X-Microsystems/xmicro-bus/Images/Gen 2/Display 1.jpg

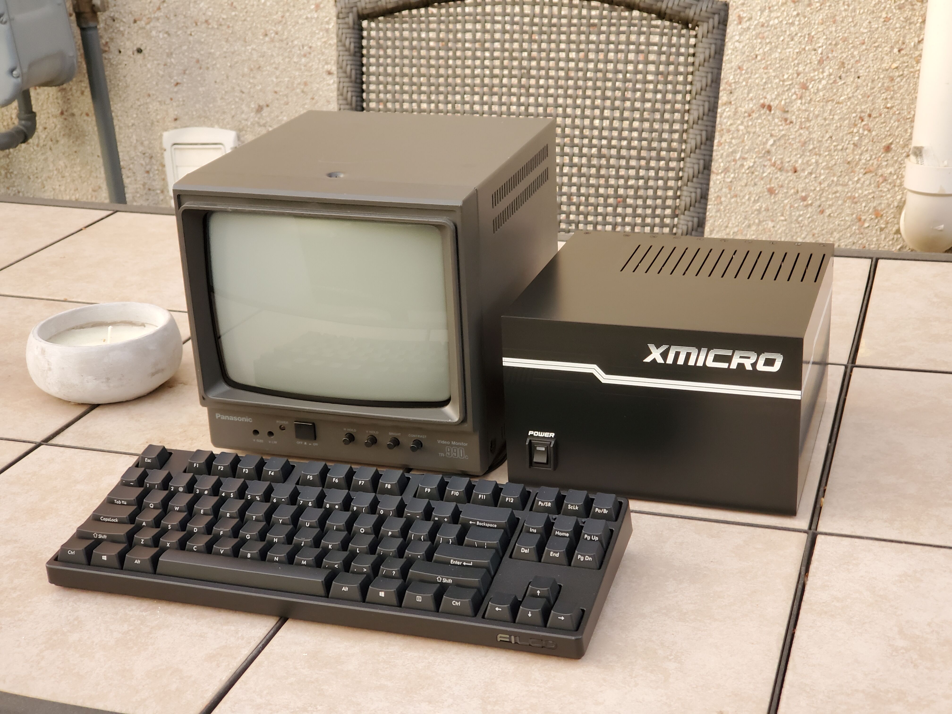
Images/Gen 2/Display 1.jpg
