X-Microsystems/xmicro-bus/Images/Gen 2/Display 2.jpg

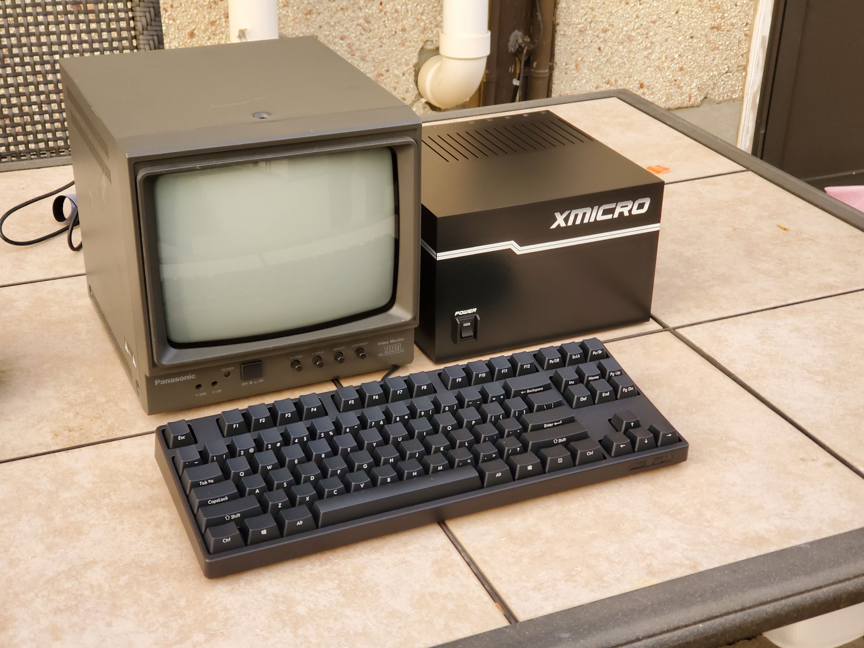
Images/Gen 2/Display 2.jpg
