X-Microsystems/xmicro-bus/Images/Gen 2/Display 3.jpg

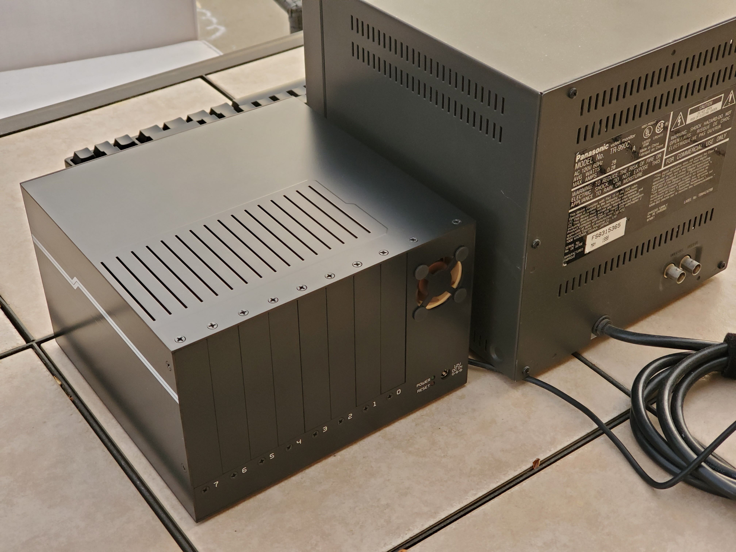
Images/Gen 2/Display 3.jpg
