X-Microsystems/xmicro-bus/Images/Gen 2/Display 5.jpg

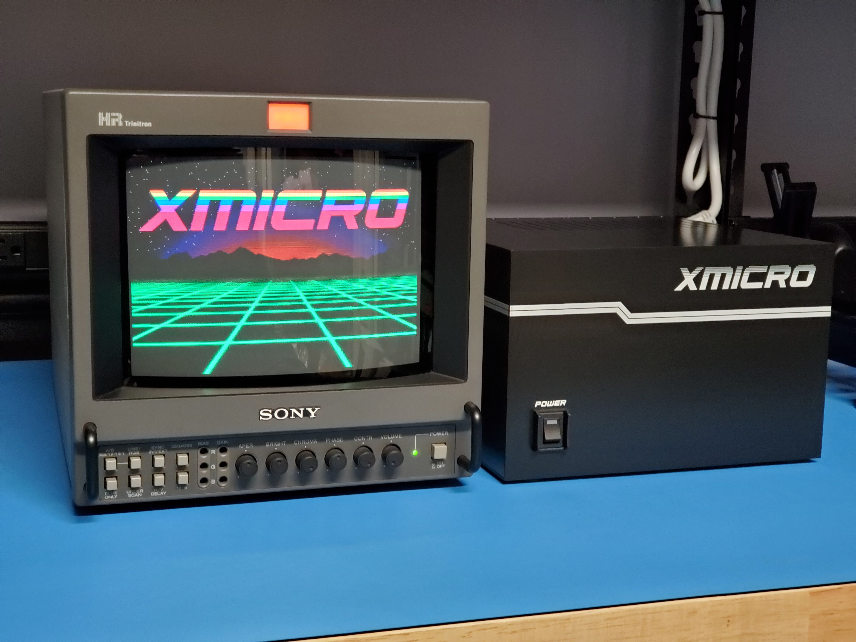
Images/Gen 2/Display 5.jpg
