X-Microsystems/xmicro-bus/Images/Gen 2/Family 2.jpg

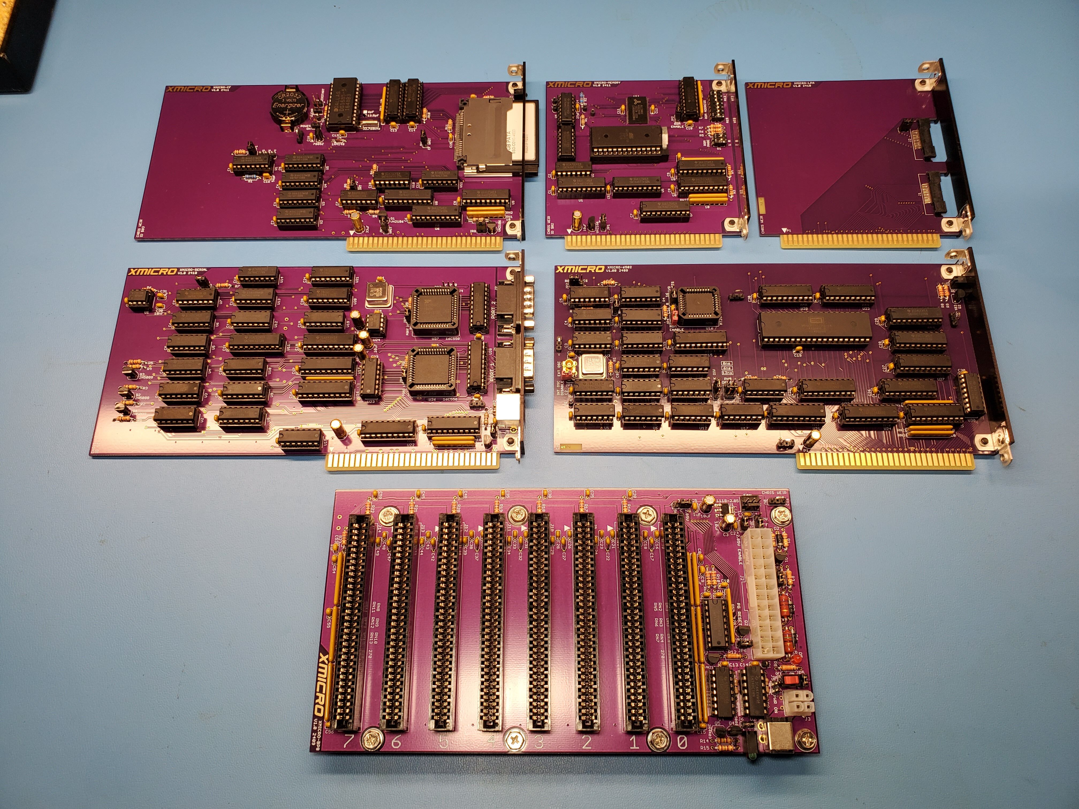
Images/Gen 2/Family 2.jpg
