X-Microsystems/xmicro-bus/Images/Gen 2/Inside 1.jpg

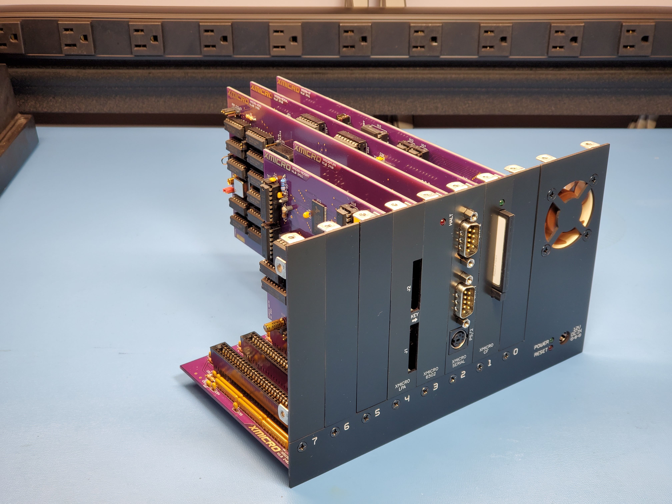
Images/Gen 2/Inside 1.jpg
