X-Microsystems/xmicro-bus/Images/Gen 2/Inside 2.jpg

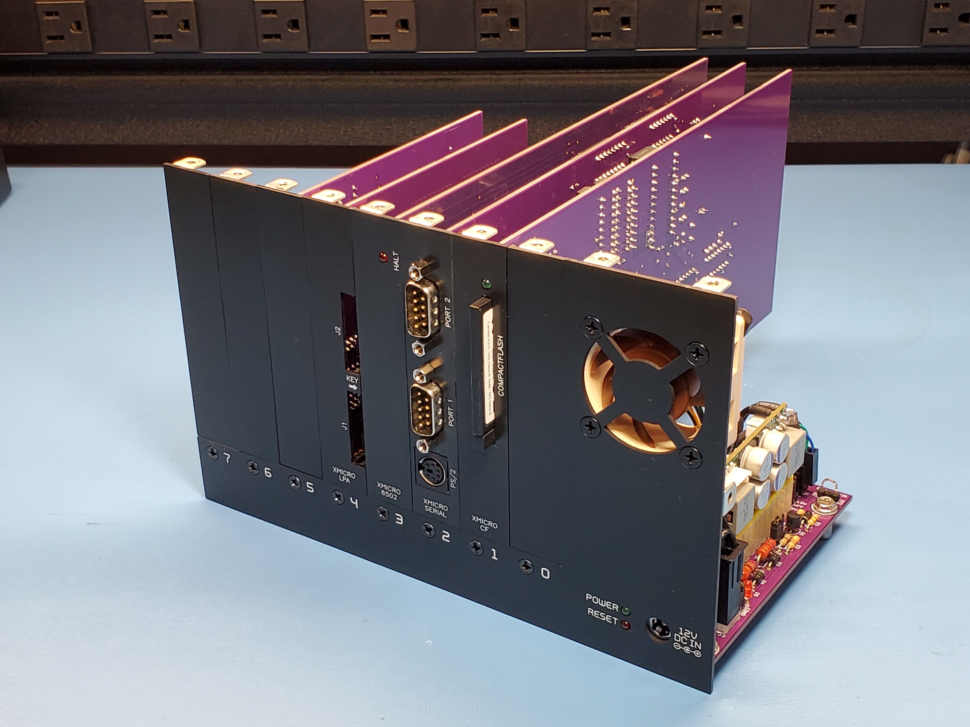
Images/Gen 2/Inside 2.jpg
