X-Microsystems/xmicro-bus/Images/Gen 2/System 1.jpg

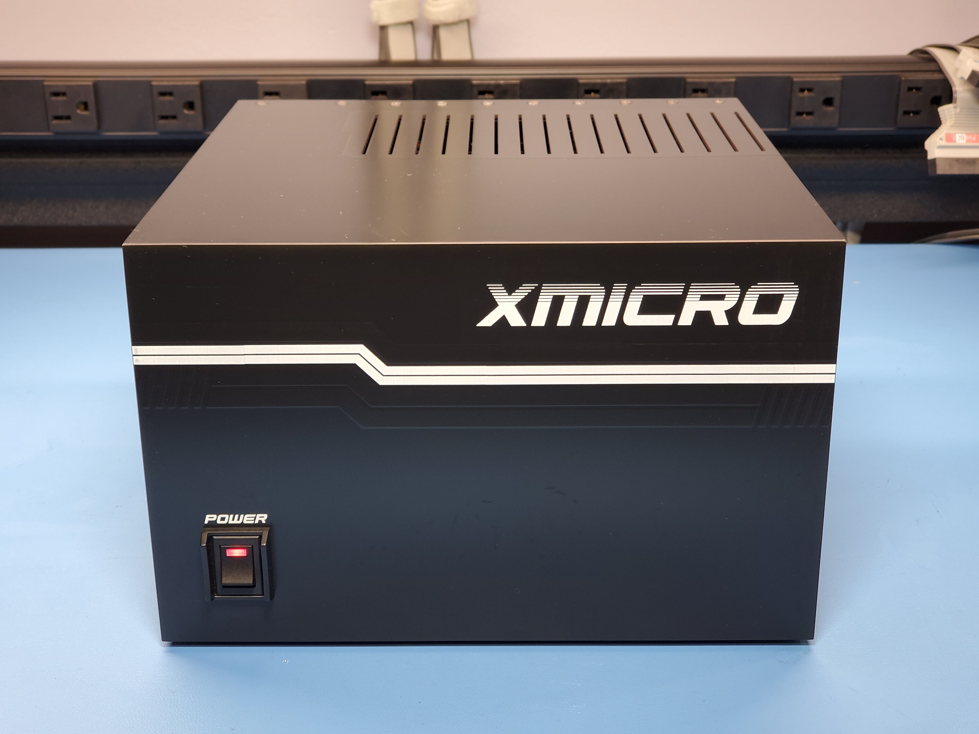
Images/Gen 2/System 1.jpg
