X-Microsystems/xmicro-bus/Images/Gen 2/System 3.jpg

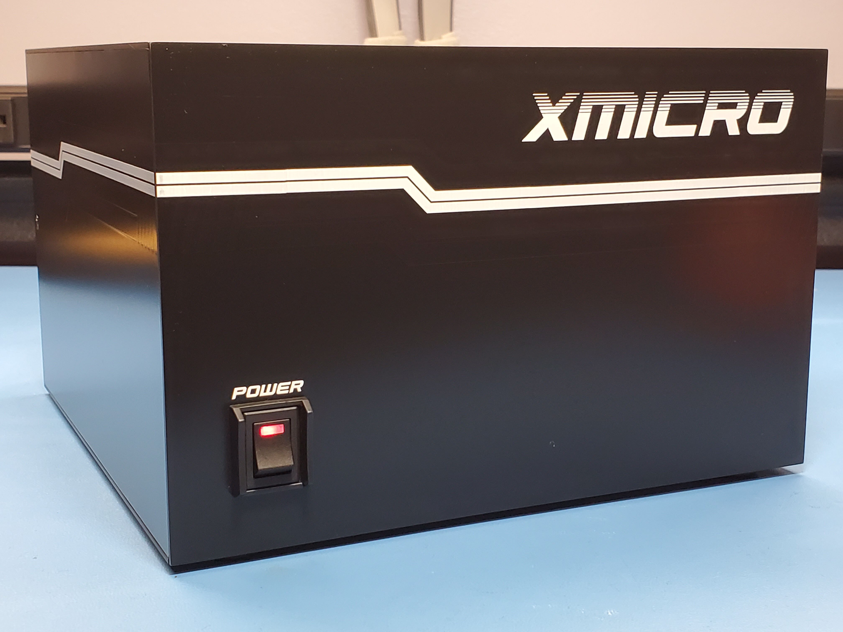
Images/Gen 2/System 3.jpg
