X-Microsystems/xmicro-bus/Images/Gen 2/Workbench 1.jpg

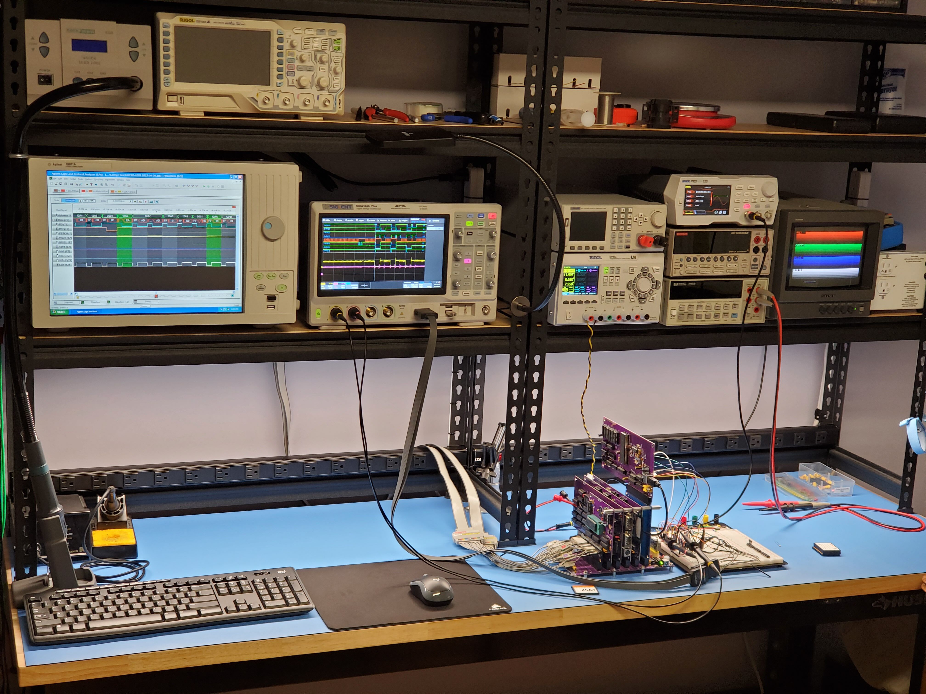
Images/Gen 2/Workbench 1.jpg
