X-Microsystems/xmicro-bus/Images/Gen 2/Workbench 2.jpg

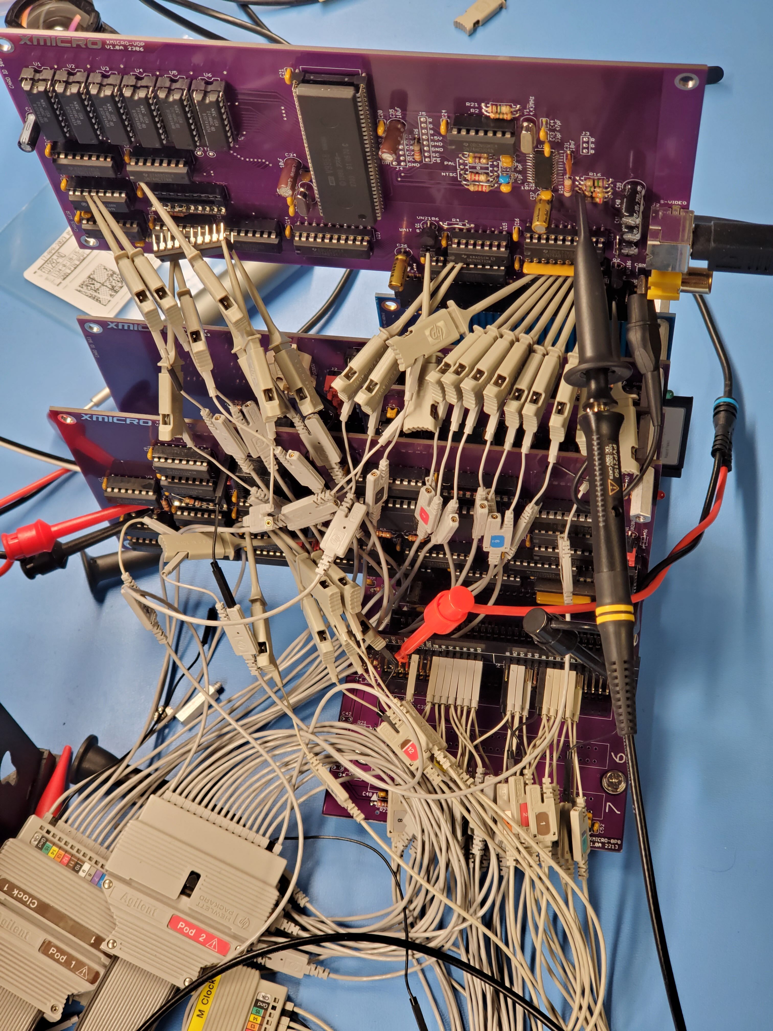
Images/Gen 2/Workbench 2.jpg
