X-Microsystems/xmicro-bus/Images/Gen 2/XMICRO-6502 2.jpg

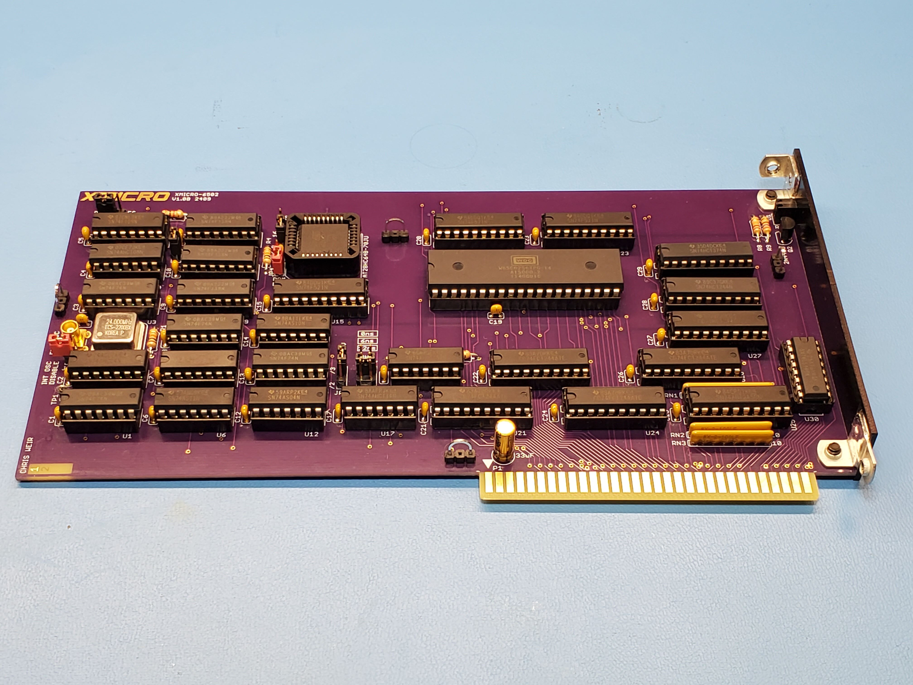
Images/Gen 2/XMICRO-6502 2.jpg
