X-Microsystems/xmicro-bus/Images/Gen 2/XMICRO-BP8 1.jpg

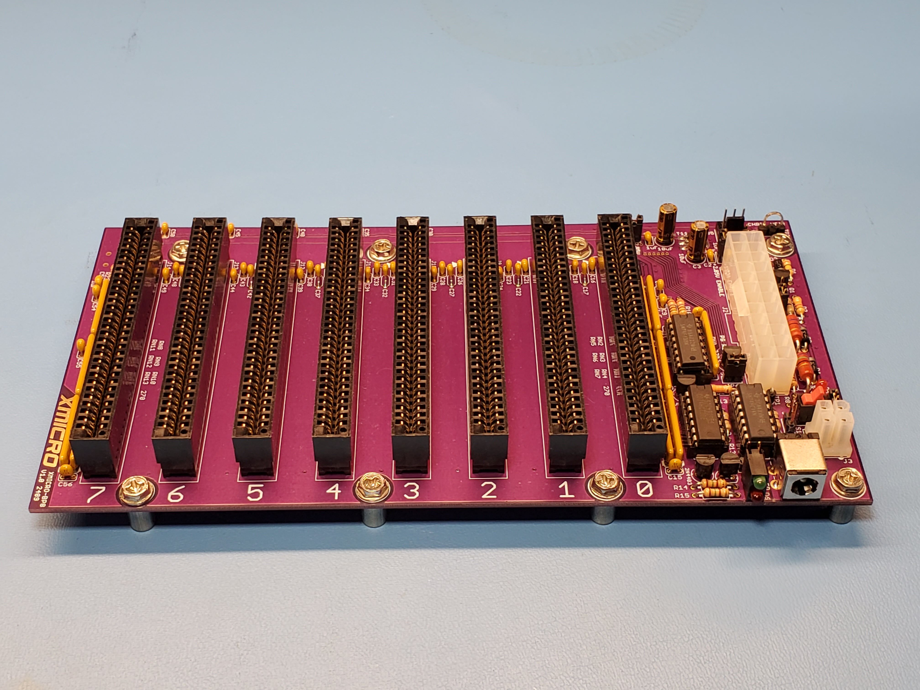
Images/Gen 2/XMICRO-BP8 1.jpg
