X-Microsystems/xmicro-bus/Images/Gen 2/XMICRO-CF 2.jpg

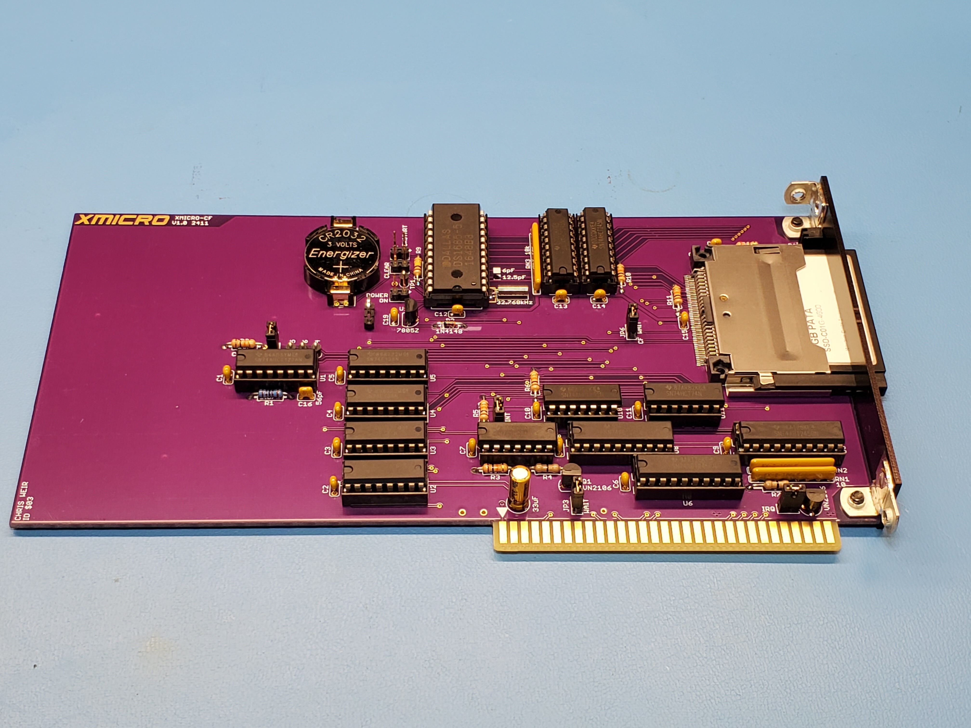
Images/Gen 2/XMICRO-CF 2.jpg
