X-Microsystems/xmicro-bus/Images/Gen 2/XMICRO-CF 3.jpg

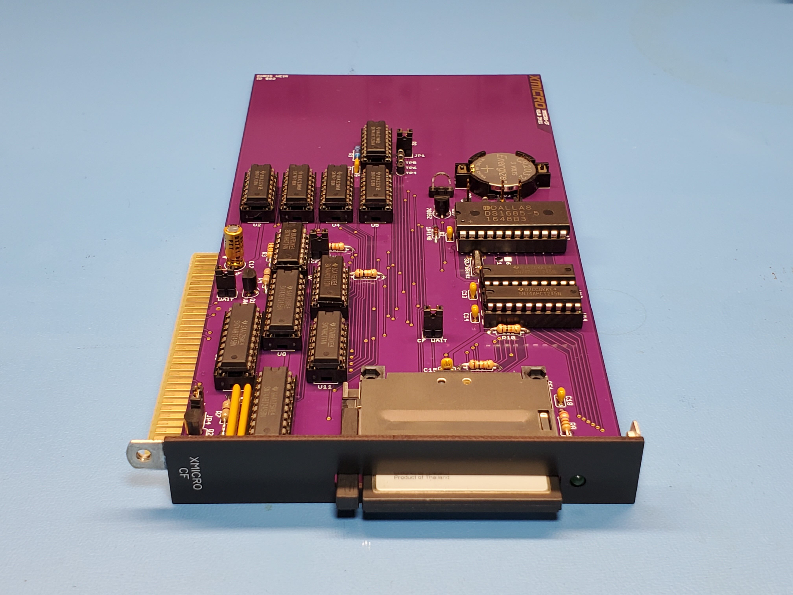
Images/Gen 2/XMICRO-CF 3.jpg
