X-Microsystems/xmicro-bus/Images/Gen 2/XMICRO-LPA 1.jpg

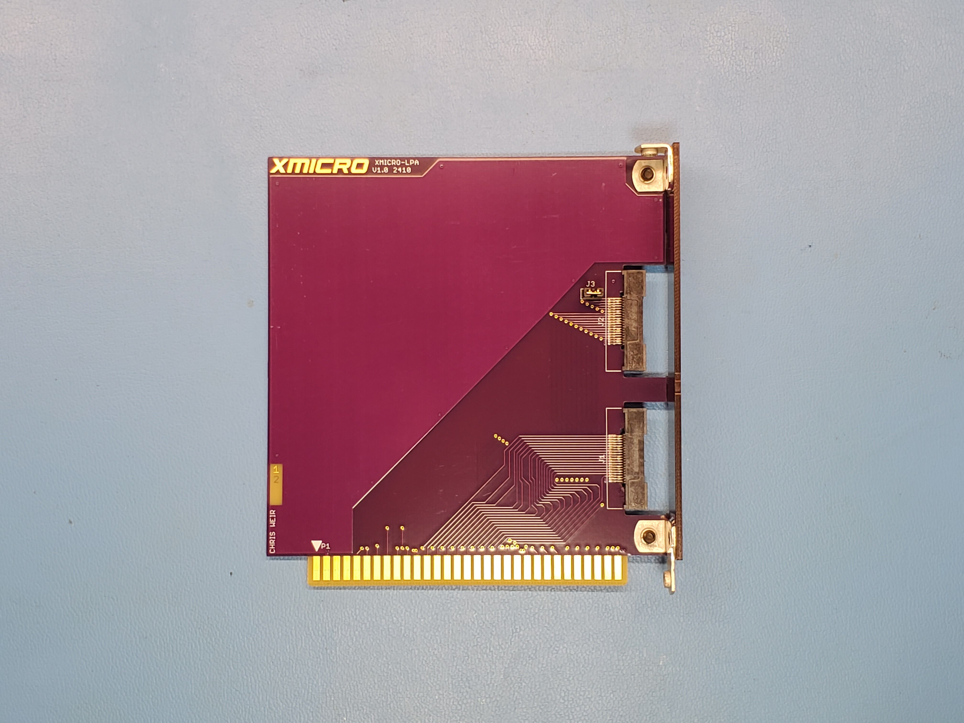
Images/Gen 2/XMICRO-LPA 1.jpg
