X-Microsystems/xmicro-bus/Images/Gen 2/XMICRO-LPA 2.jpg

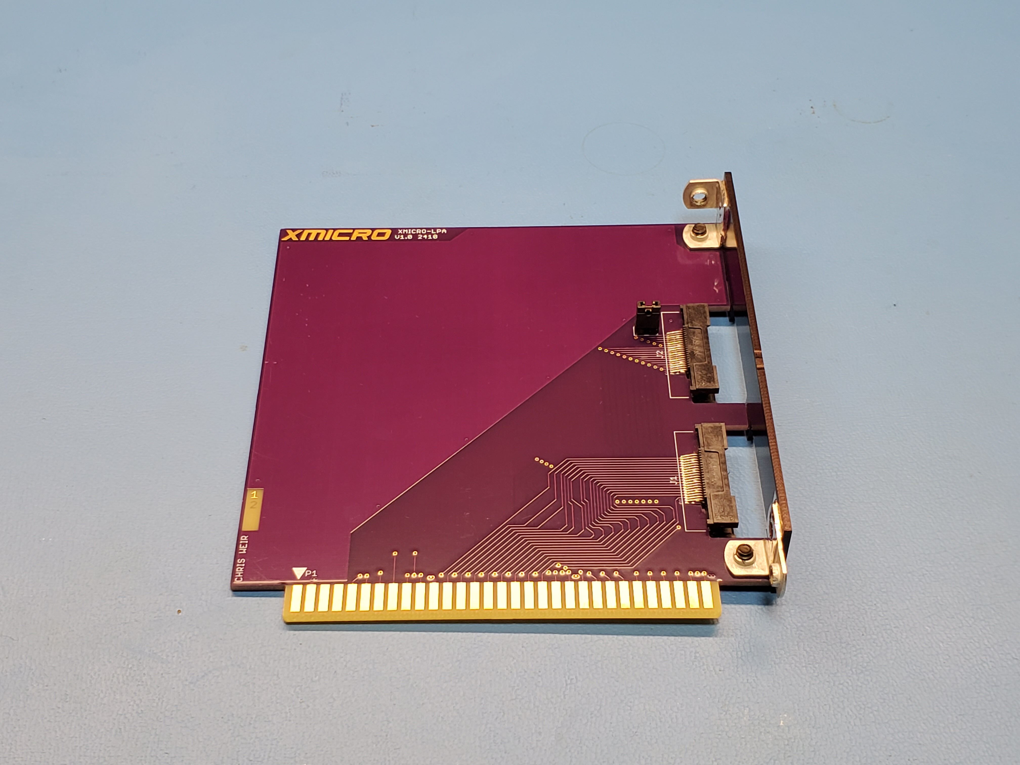
Images/Gen 2/XMICRO-LPA 2.jpg
