X-Microsystems/xmicro-bus/Images/Gen 2/XMICRO-MEMORY 2.jpg

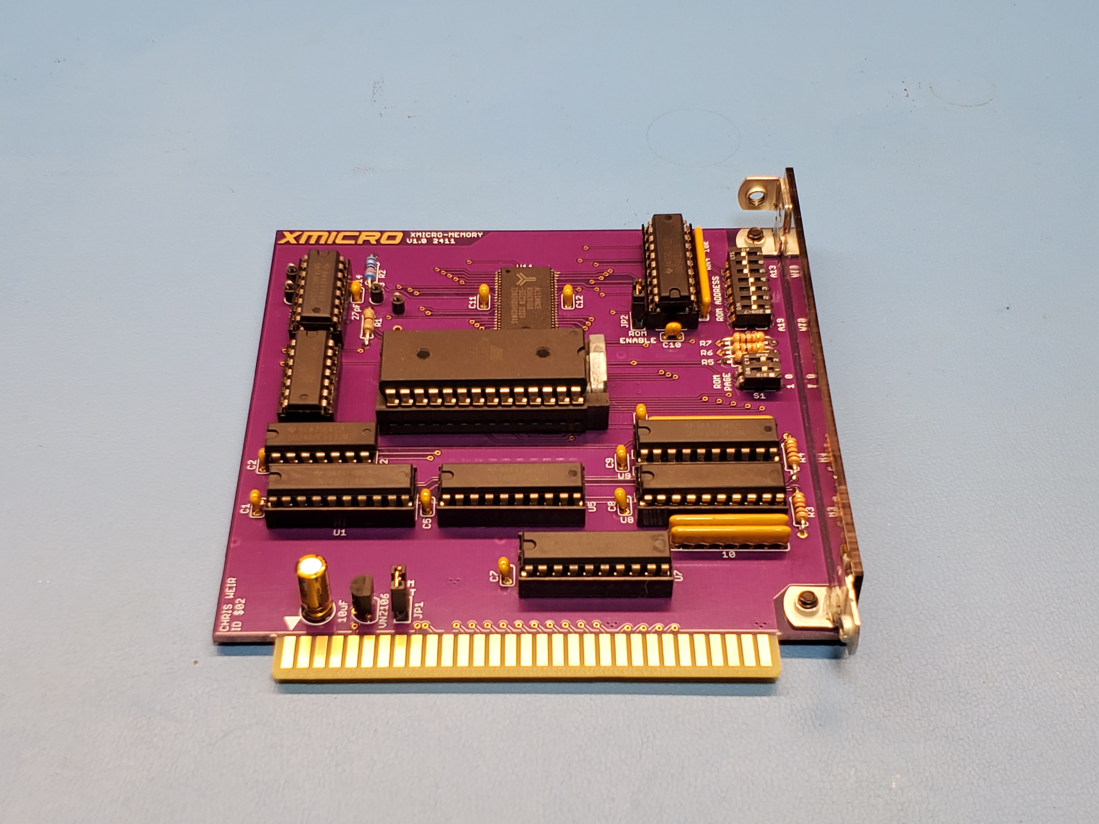
Images/Gen 2/XMICRO-MEMORY 2.jpg
