X-Microsystems/xmicro-bus/Images/Gen 2/XMICRO-SERIAL 1.jpg

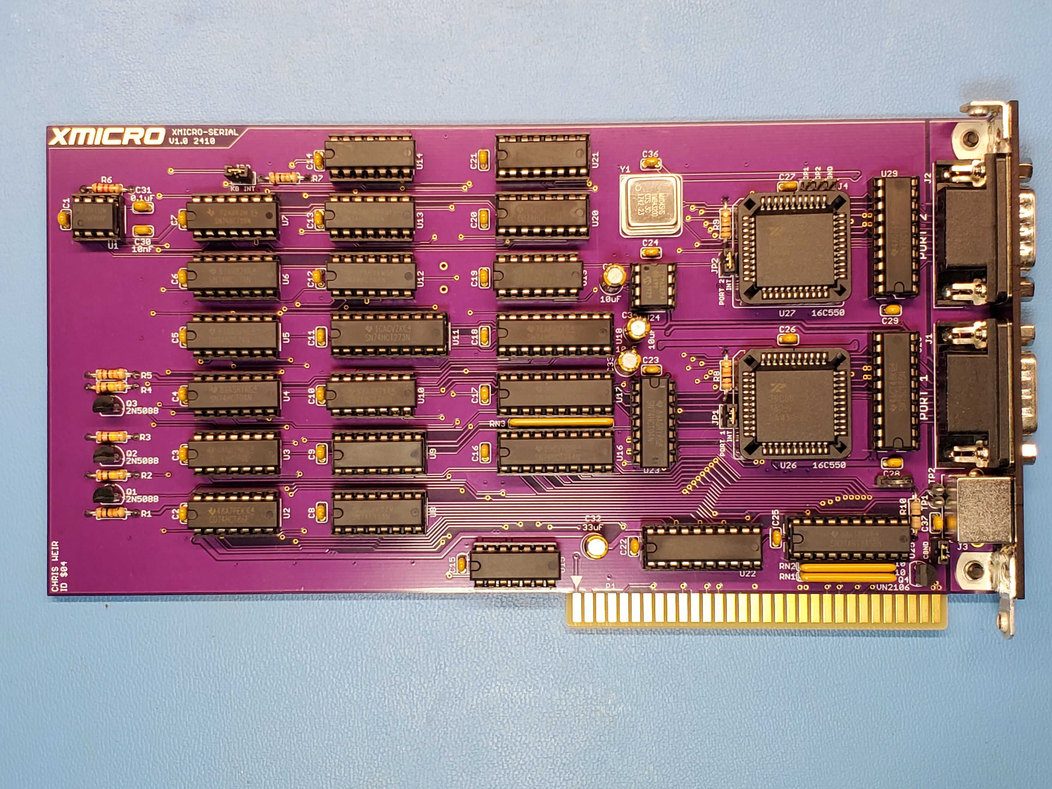
Images/Gen 2/XMICRO-SERIAL 1.jpg
