X-Microsystems/xmicro-bus/Images/Gen 2/XMICRO-SERIAL 2.jpg

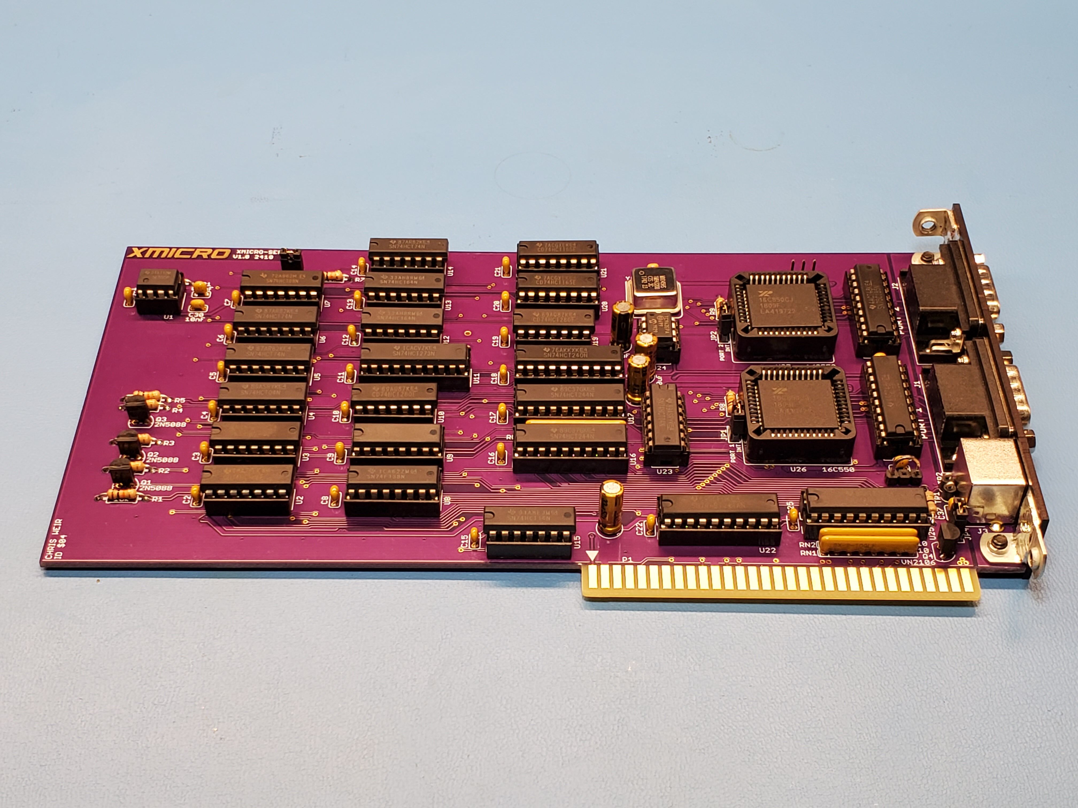
Images/Gen 2/XMICRO-SERIAL 2.jpg
