X-Microsystems/xmicro-bus/Images/Gen 2/XMICRO-SERIAL 3.jpg

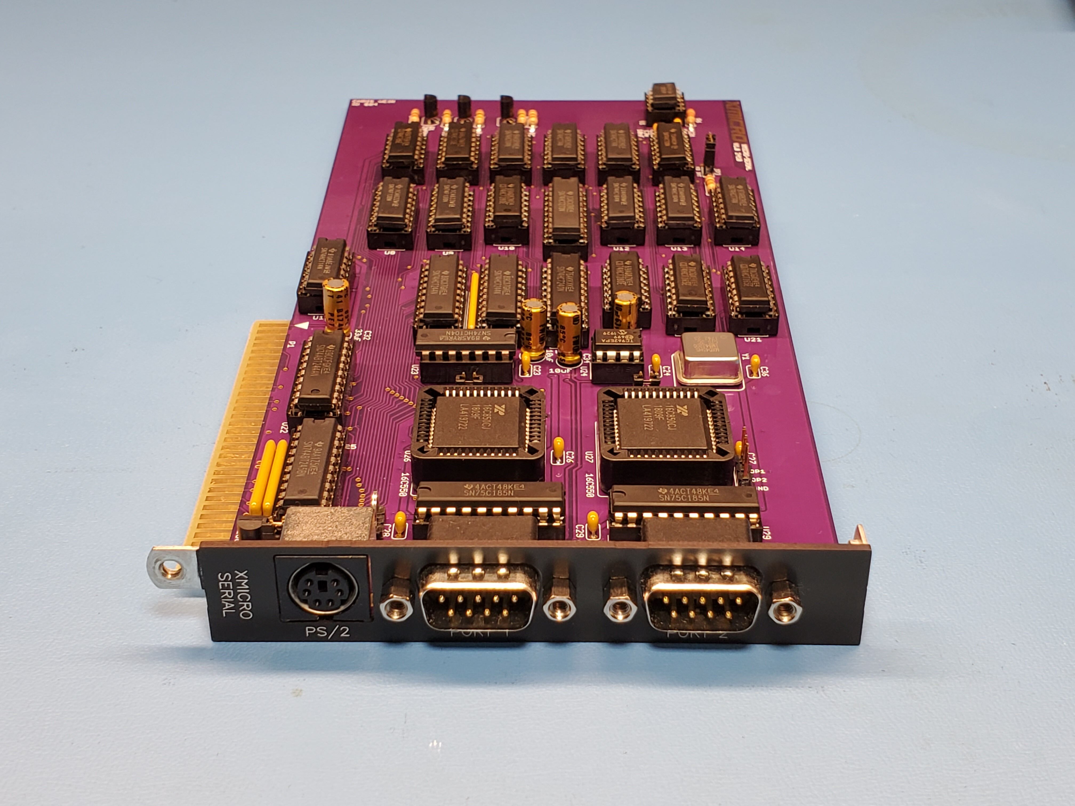
Images/Gen 2/XMICRO-SERIAL 3.jpg
